Toeloe007/A320FCU/Part 1 - Rotary Buttons/Images/image1.jpeg

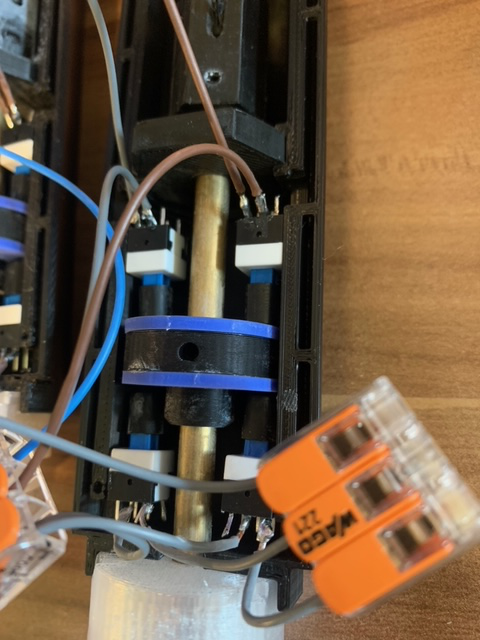
Part 1 - Rotary Buttons/Images/image1.jpeg
