Toeloe007/A320FCU/Part 1 - Rotary Buttons/Images/image2.jpeg

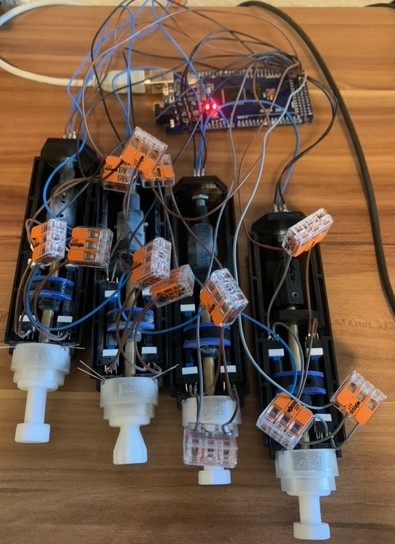
Part 1 - Rotary Buttons/Images/image2.jpeg
