Toeloe007/A320FCU/Part 2 - Buttons 7Segment Case/Images/image1.jpeg

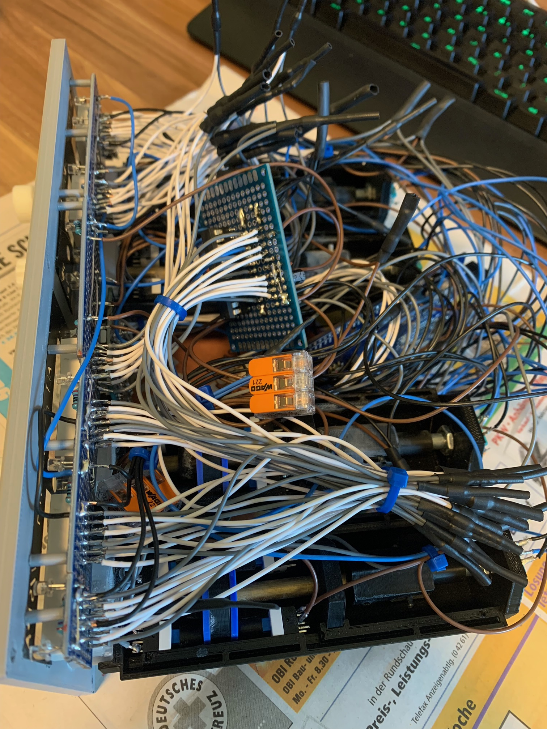
Part 2 - Buttons 7Segment Case/Images/image1.jpeg
