Toeloe007/A320FCU/Part 1 - Rotary Buttons/3D Files/1x white Speed Knob.stl

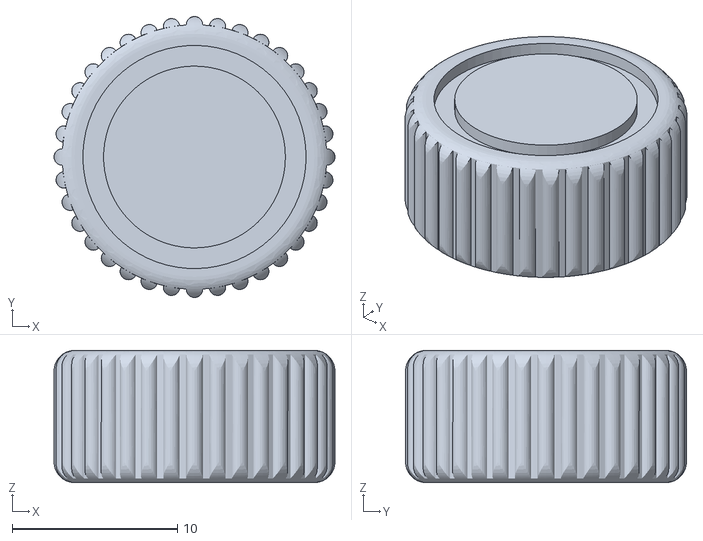
[picture p24: CAD file, 2023-08-21]
Part 1 - Rotary Buttons/3D Files/1x white Speed Knob.stl
17.0 x 17.0 x 8.00
