Toeloe007/A320FCU/Part 2 - Buttons 7Segment Case/3D Files/3x11Display Pin.stl

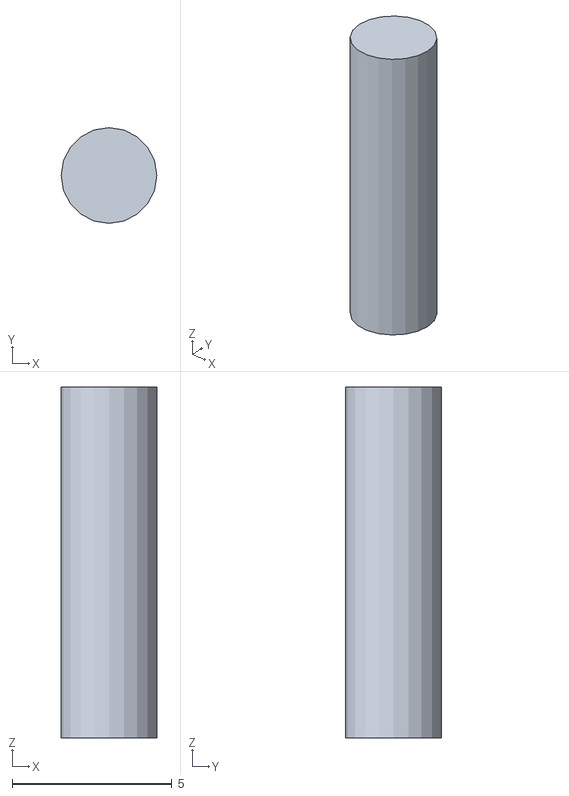
[picture p25: CAD file, 2023-09-04]
Part 2 - Buttons 7Segment Case/3D Files/3x11Display Pin.stl
3.00 x 3.00 x 11.0
