Toeloe007/A320FCU/Part 1 - Rotary Buttons/3D Files/4x black Encoder Slide.stl

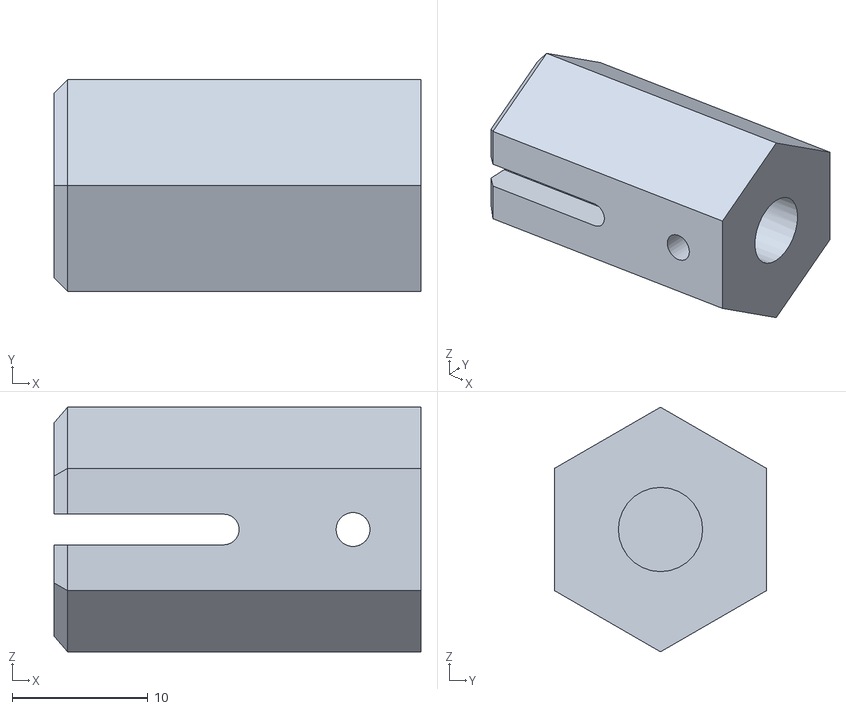
[picture p26: CAD file, 2023-08-21]
Part 1 - Rotary Buttons/3D Files/4x black Encoder Slide.stl
27.0 x 15.6 x 18.0
