Toeloe007/A320FCU/Part 2 - Buttons 7Segment Case/3D Files/ATHR_Text_smaller.stl

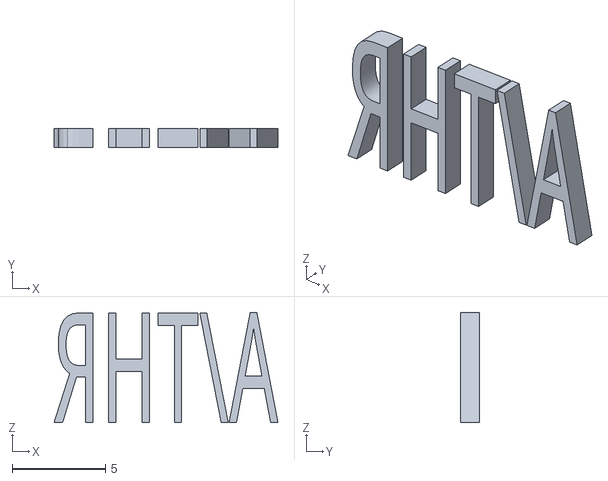
[picture p27: CAD file, 2023-09-04]
Part 2 - Buttons 7Segment Case/3D Files/ATHR_Text_smaller.stl
12.0 x 1 x 5.90
