Toeloe007/A320FCU/Part 1 - Rotary Buttons/3D Files/1x white ALT Knob .stl

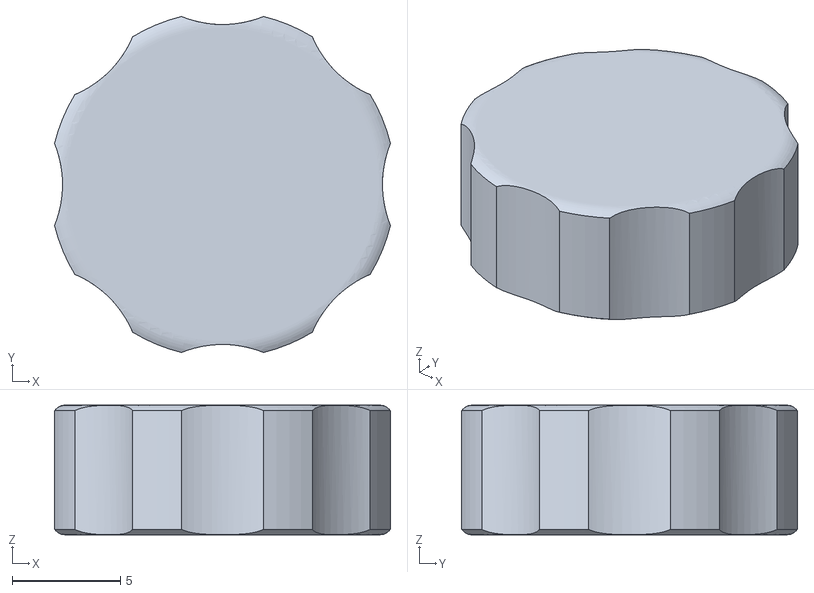
[picture p28: CAD file, 2023-08-21]
Part 1 - Rotary Buttons/3D Files/1x white ALT Knob .stl
15.5 x 15.5 x 6.00
