Toeloe007/A320FCU/Part 2 - Buttons 7Segment Case/3D Files/AP1_Btn_smaller.stl

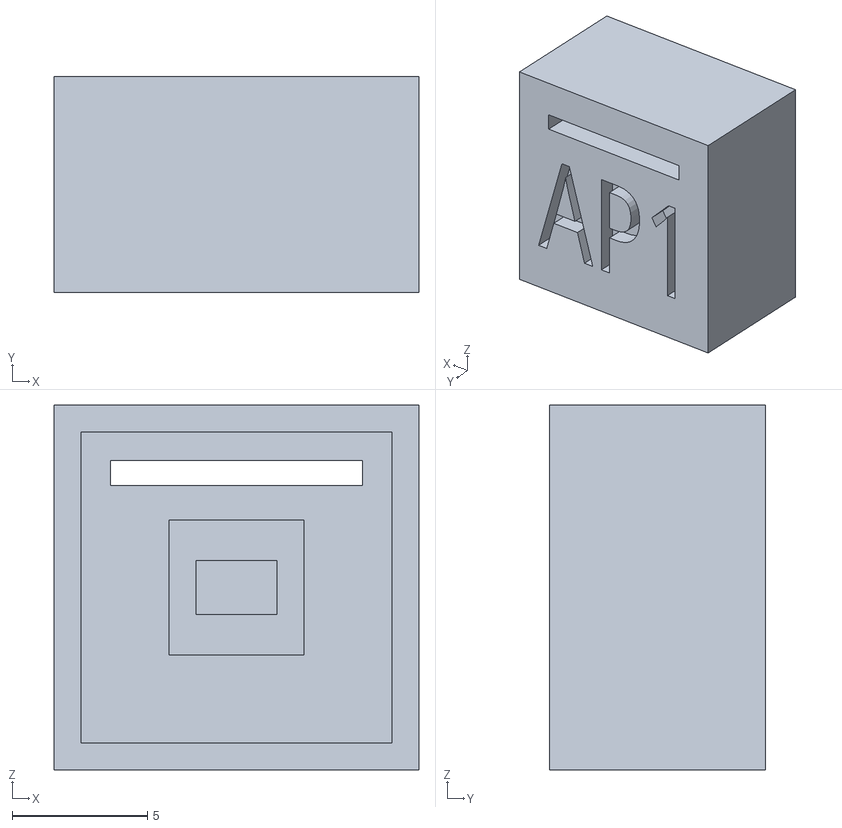
[picture p29: CAD file, 2023-09-04]
Part 2 - Buttons 7Segment Case/3D Files/AP1_Btn_smaller.stl
13.5 x 8.00 x 13.5
