Toeloe007/A320FCU/Part 1 - Rotary Buttons/3D Files/4x black  Push Pull Disc.stl

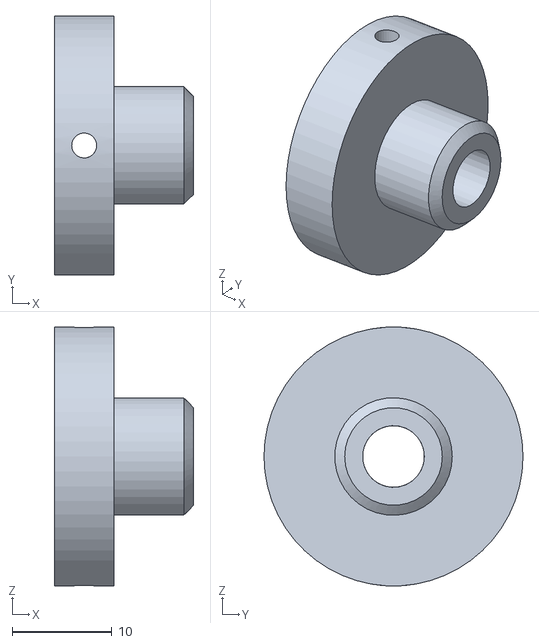
[picture p30: CAD file, 2023-08-21]
Part 1 - Rotary Buttons/3D Files/4x black Push Pull Disc.stl
14.0 x 26.0 x 26.0
