Toeloe007/A320FCU/Part 2 - Buttons 7Segment Case/3D Files/5x11Display Pin.stl

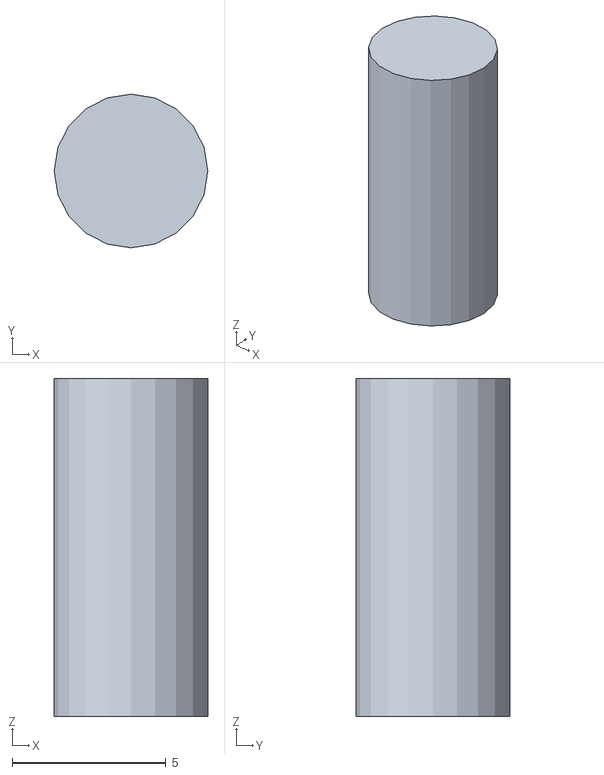
[picture p31: CAD file, 2023-09-04]
Part 2 - Buttons 7Segment Case/3D Files/5x11Display Pin.stl
5.00 x 5.00 x 11.0
