Toeloe007/A320FCU/Part 2 - Buttons 7Segment Case/3D Files/AP2_Text_smaller.stl

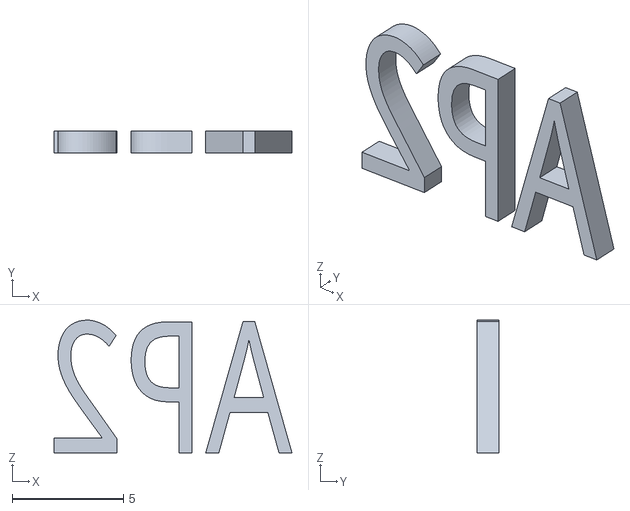
[picture p33: CAD file, 2023-09-04]
Part 2 - Buttons 7Segment Case/3D Files/AP2_Text_smaller.stl
10.7 x 1.00 x 5.96
