Toeloe007/A320FCU/Part 2 - Buttons 7Segment Case/3D Files/box.stl

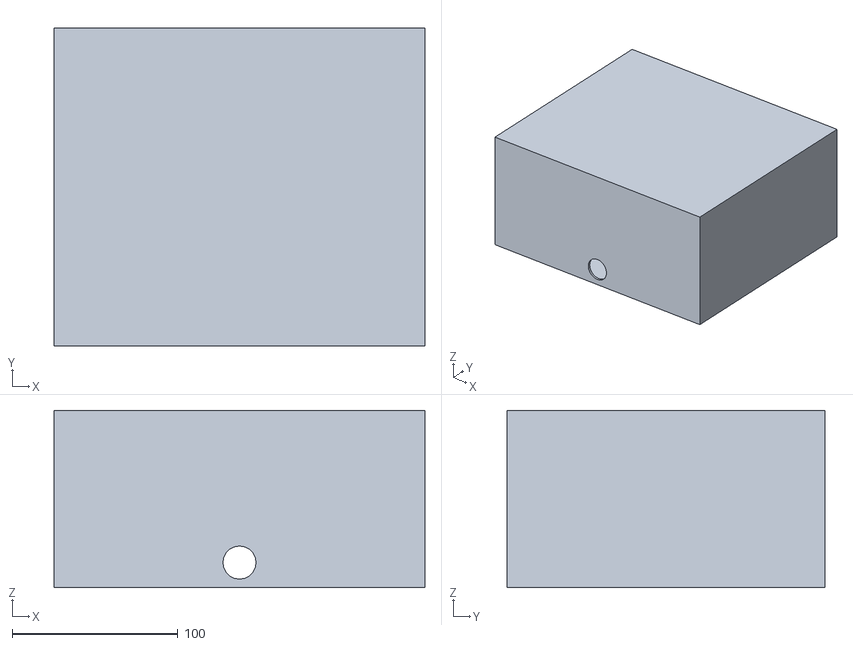
[picture p35: CAD file, 2023-09-04]
Part 2 - Buttons 7Segment Case/3D Files/box.stl
224.0 x 192.0 x 107.0
