Toeloe007/A320FCU/Part 2 - Buttons 7Segment Case/3D Files/AP1_Text_smaller.stl

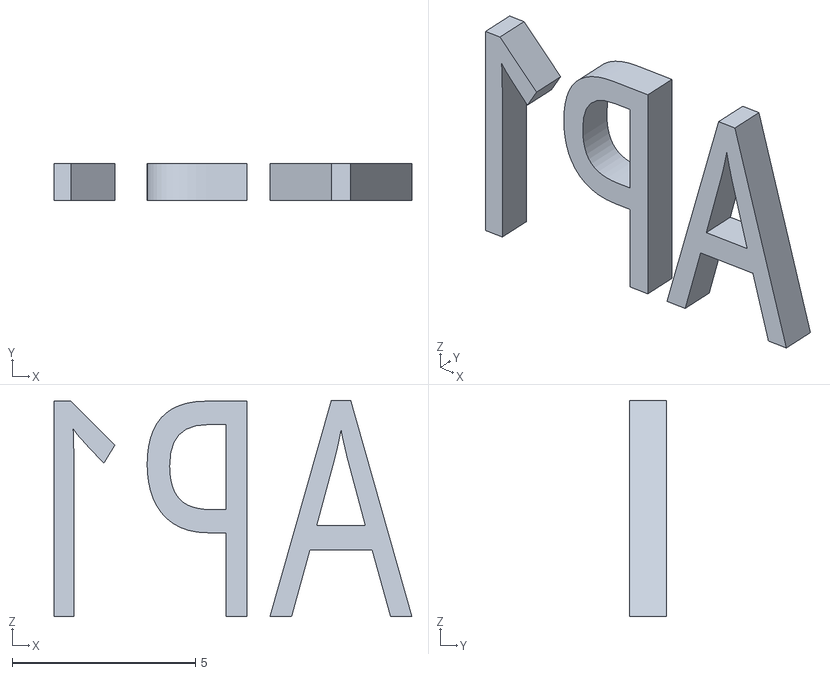
[picture p36: CAD file, 2023-09-04]
Part 2 - Buttons 7Segment Case/3D Files/AP1_Text_smaller.stl
9.76 x 1.00 x 5.90
