Toeloe007/A320FCU/Part 2 - Buttons 7Segment Case/3D Files/BoxPowerSupply_Ring.stl

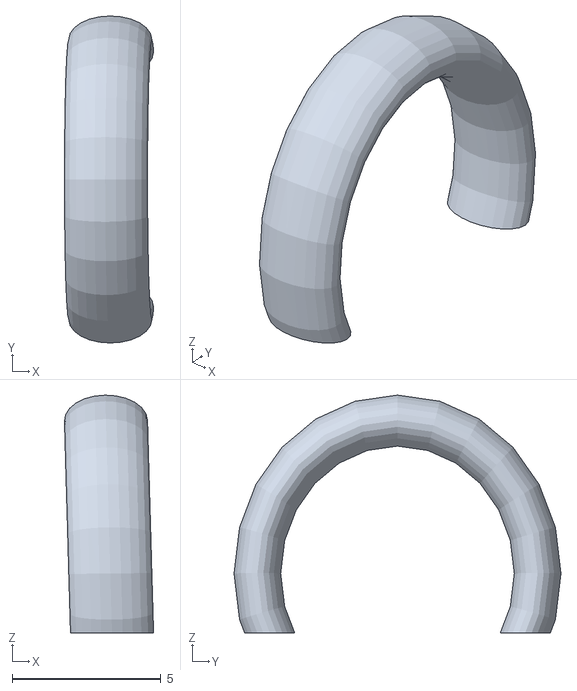
[picture p37: CAD file, 2023-08-30]
Part 2 - Buttons 7Segment Case/3D Files/BoxPowerSupply_Ring.stl
3.00 x 11.0 x 8.00
