Toeloe007/A320FCU/Part 2 - Buttons 7Segment Case/3D Files/1000_Text.stl

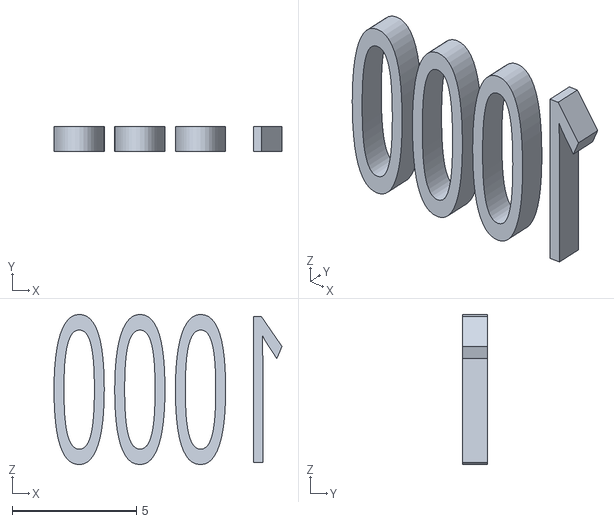
[picture p40: CAD file, 2023-08-30]
Part 2 - Buttons 7Segment Case/3D Files/1000_Text.stl
9.18 x 1.00 x 6.05
