Toeloe007/A320FCU/Part 2 - Buttons 7Segment Case/3D Files/EXPED_Text.stl

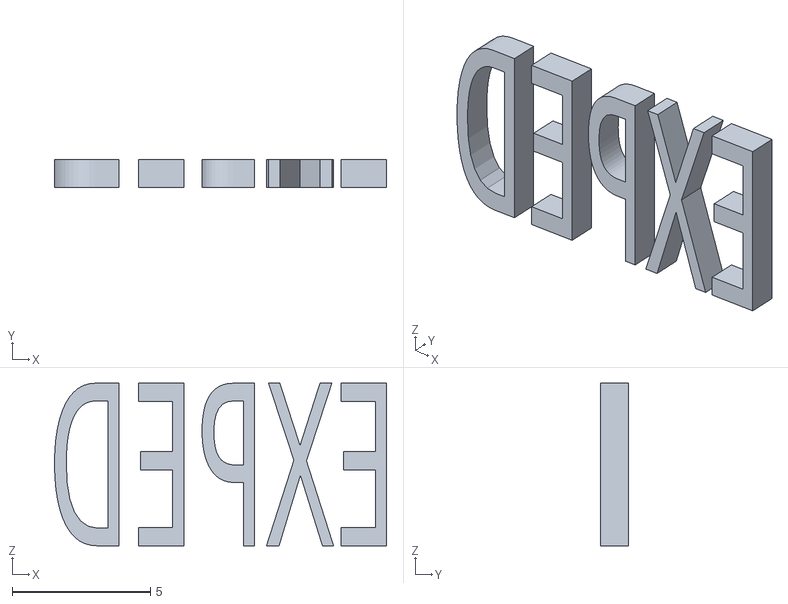
[picture p41: CAD file, 2023-08-30]
Part 2 - Buttons 7Segment Case/3D Files/EXPED_Text.stl
12.0 x 1.00 x 5.88
