Toeloe007/A320FCU/Part 2 - Buttons 7Segment Case/3D Files/LOC_Text.stl

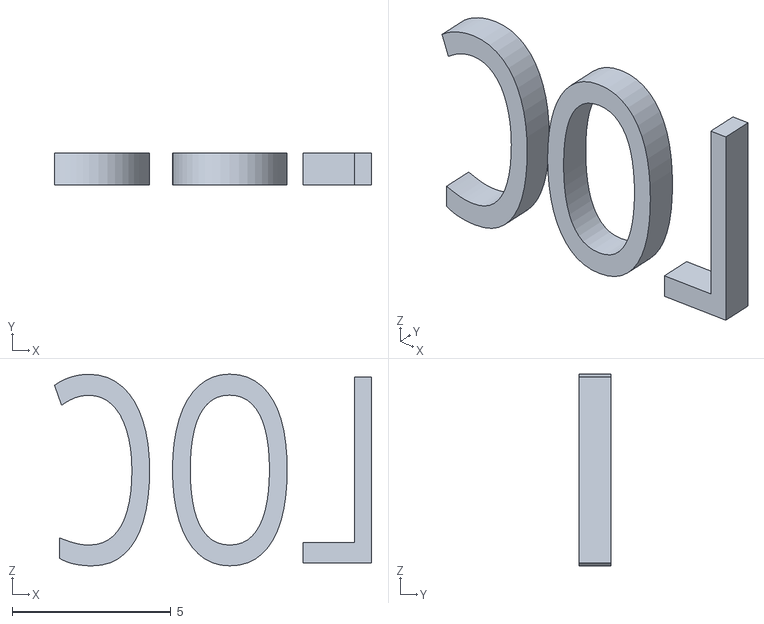
[picture p42: CAD file, 2023-08-30]
Part 2 - Buttons 7Segment Case/3D Files/LOC_Text.stl
10.0 x 1.00 x 6.05
