Toeloe007/A320FCU/Part 2 - Buttons 7Segment Case/3D Files/APPR_Text.stl

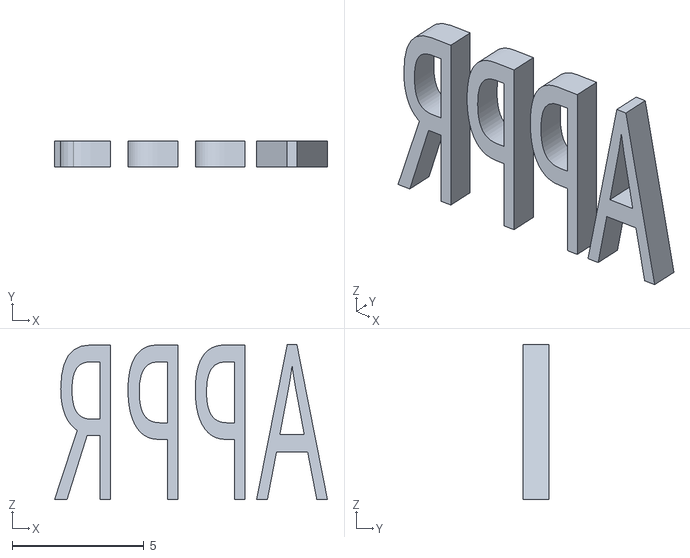
[picture p43: CAD file, 2023-08-30]
Part 2 - Buttons 7Segment Case/3D Files/APPR_Text.stl
10.4 x 1.00 x 5.90
