Toeloe007/A320FCU/Part 2 - Buttons 7Segment Case/3D Files/BoxPowerSupply_Bottom.stl

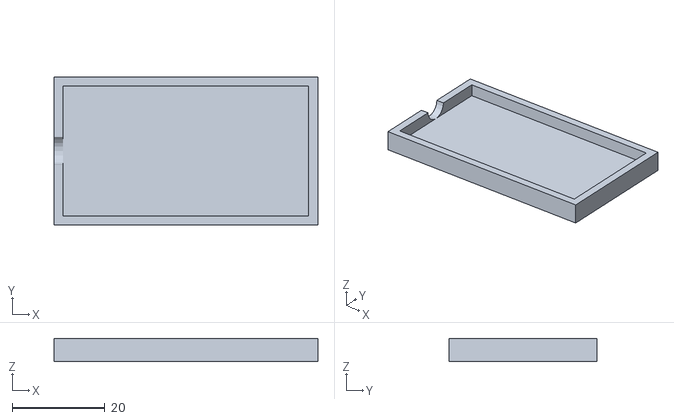
[picture p44: CAD file, 2023-08-30]
Part 2 - Buttons 7Segment Case/3D Files/BoxPowerSupply_Bottom.stl
57.0 x 32.0 x 5.00
