Toeloe007/A320FCU/Part 2 - Buttons 7Segment Case/3D Files/BTN_Black_round.stl

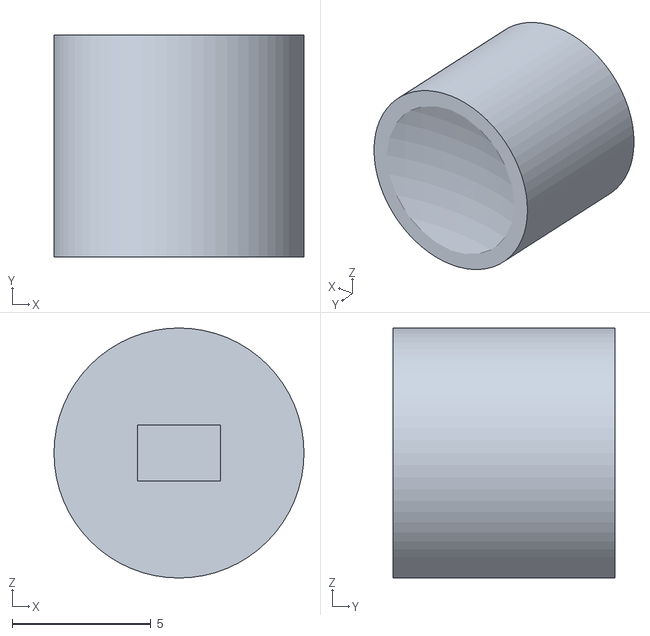
[picture p45: CAD file, 2023-08-30]
Part 2 - Buttons 7Segment Case/3D Files/BTN_Black_round.stl
9.00 x 8.00 x 9.00
