Toeloe007/A320FCU/Part 2 - Buttons 7Segment Case/3D Files/Front_5mm50infill.stl

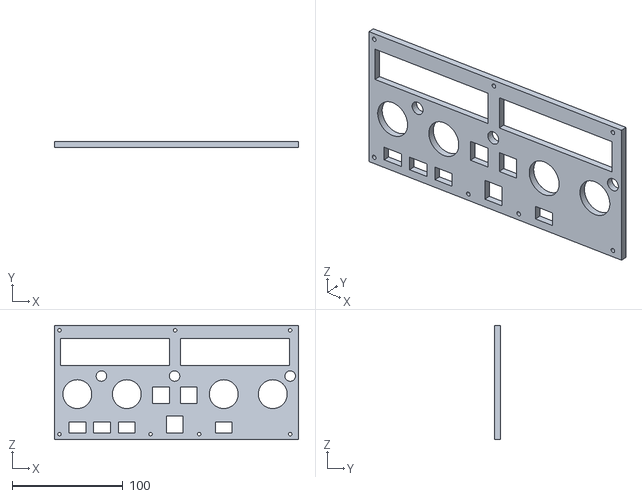
[picture p47: CAD file, 2023-08-30]
Part 2 - Buttons 7Segment Case/3D Files/Front_5mm50infill.stl
220.0 x 5.00 x 103.0
