Toeloe007/A320FCU/Part 2 - Buttons 7Segment Case/3D Files/EXPED_Btn.stl

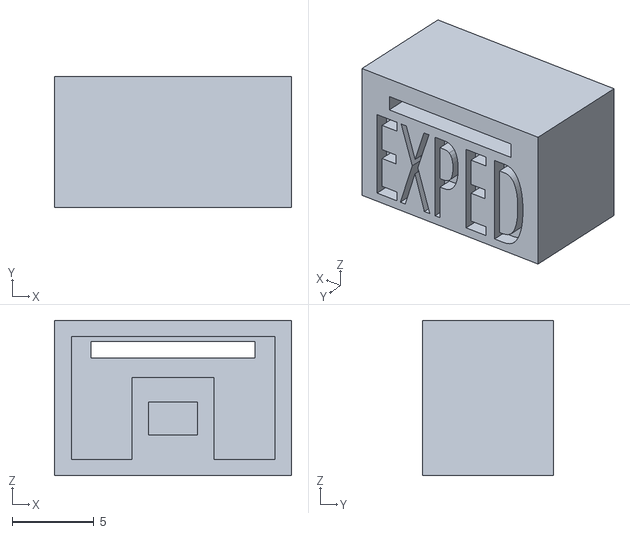
[picture p48: CAD file, 2023-08-30]
Part 2 - Buttons 7Segment Case/3D Files/EXPED_Btn.stl
14.5 x 8.00 x 9.50
