Toeloe007/A320FCU/Part 2 - Buttons 7Segment Case/3D Files/BoxPowerSupply_Top.stl

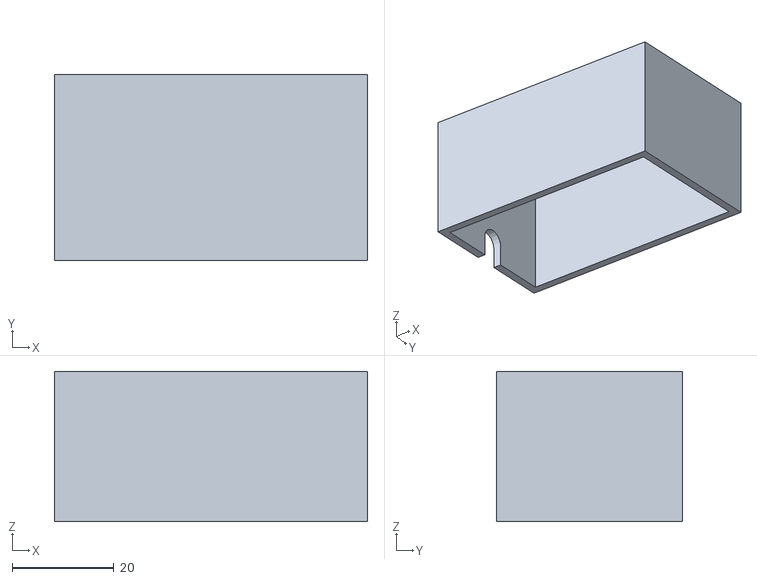
[picture p49: CAD file, 2023-08-30]
Part 2 - Buttons 7Segment Case/3D Files/BoxPowerSupply_Top.stl
61.5 x 36.5 x 29.5
